akinbender/open-smartwatch-spy/3d/rugged box/stls/hinge v1.STL

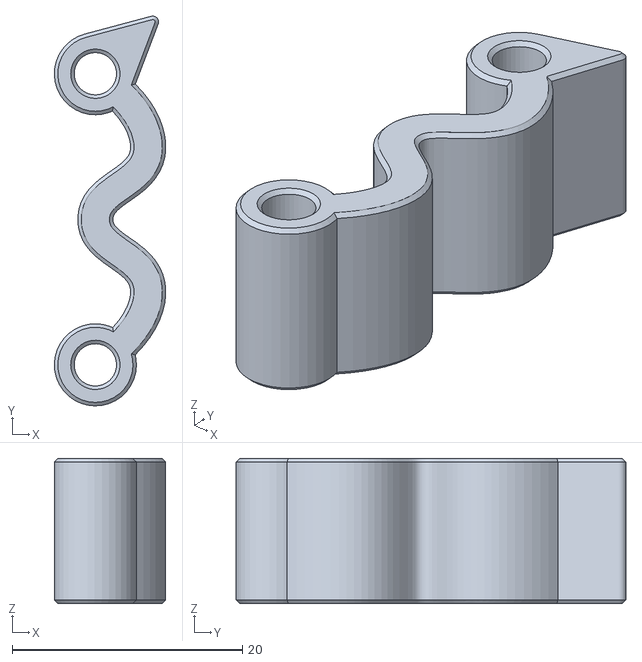
[picture p15: CAD file, 2022-03-14]
3d/rugged box/stls/hinge v1.STL
9.68 x 33.9 x 12.6
