akinbender/open-smartwatch-spy/3d/spywatch/bottom_subassembly/bottom_shell.SLDPRT

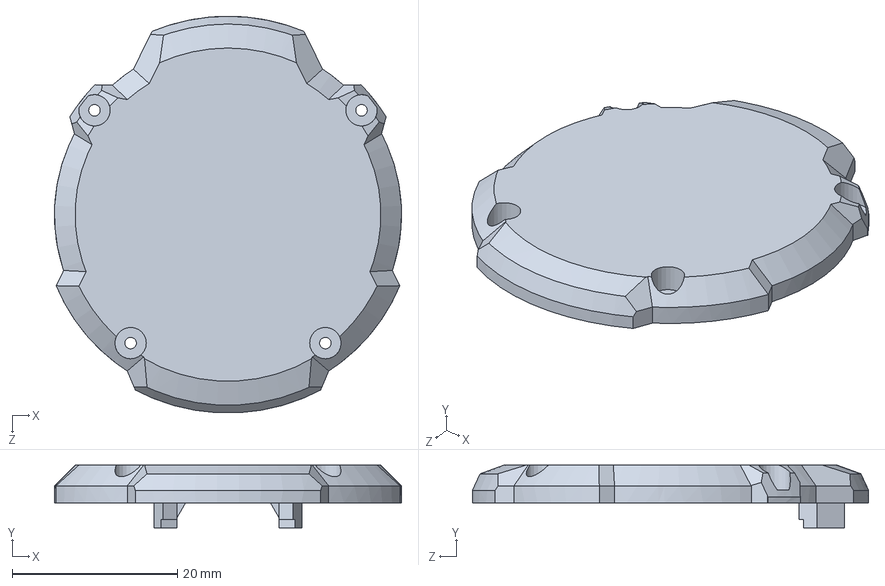
[picture p16: CAD file, 2022-03-14]
3d/spywatch/bottom_subassembly/bottom_shell.SLDPRT
42.0 x 7.60 x 48.0 mm
