akinbender/open-smartwatch-spy/3d/spywatch/common/middle_payload_test.SLDPRT

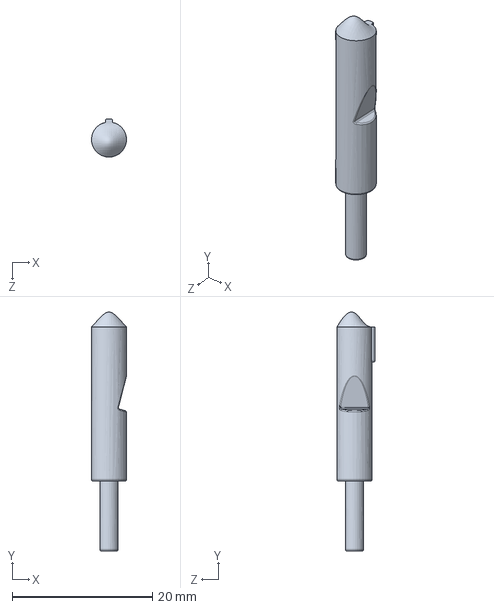
[picture p17: CAD file, 2022-03-14]
3d/spywatch/common/middle_payload_test.SLDPRT
5.00 x 34.1 x 5.45 mm
