akinbender/open-smartwatch-spy/3d/spywatch/middle_subassembly_fail1/middle_release_trigger.SLDPRT

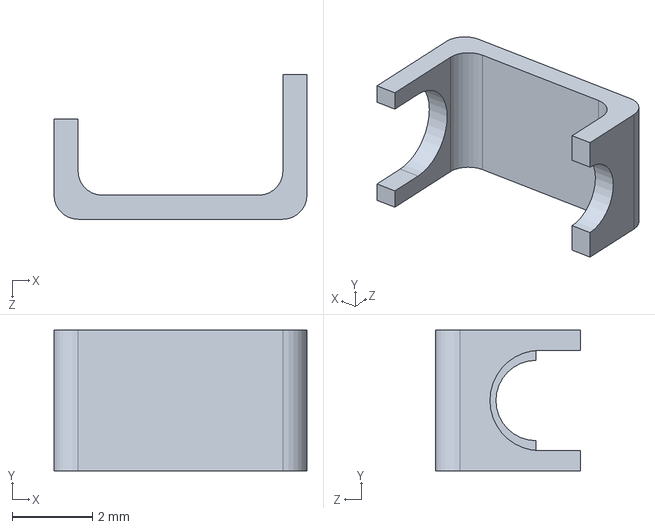
[picture p18: CAD file, 2022-03-14]
3d/spywatch/middle_subassembly_fail1/middle_release_trigger.SLDPRT
6.30 x 3.50 x 3.60 mm
