akinbender/open-smartwatch-spy/3d/spywatch/middle_subassembly_fail1/stl/middle_payload_dart.STL

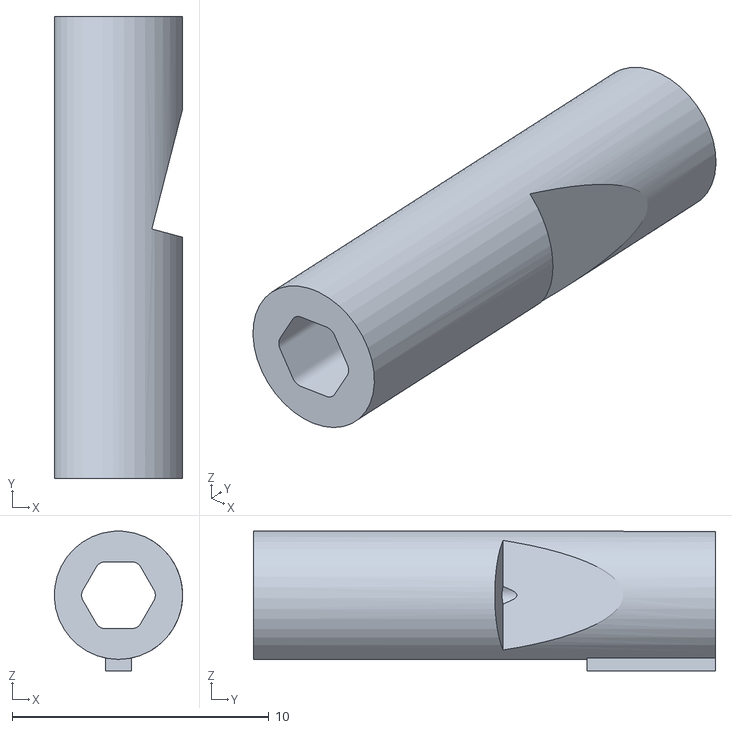
[picture p19: CAD file, 2022-03-14]
3d/spywatch/middle_subassembly_fail1/stl/middle_payload_dart.STL
5.00 x 18.0 x 5.45
