akinbender/open-smartwatch-spy/3d/spywatch/top_subassembly/top_lcd.SLDPRT

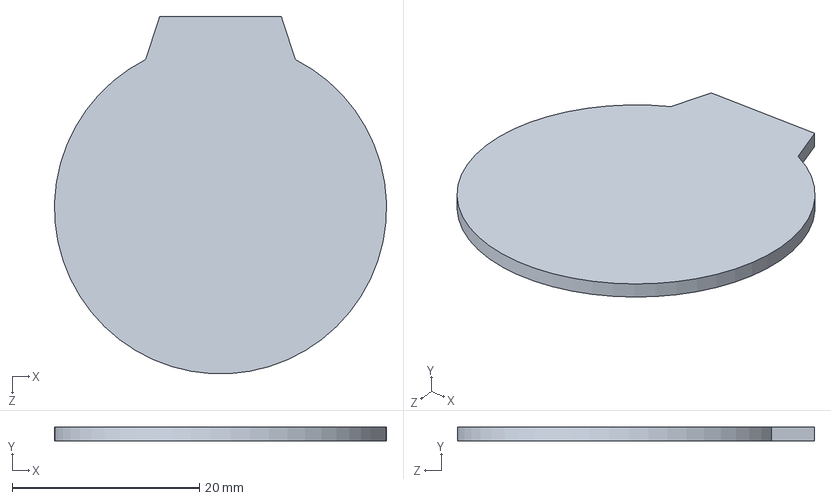
[picture p20: CAD file, 2022-03-14]
3d/spywatch/top_subassembly/top_lcd.SLDPRT
35.5 x 1.50 x 38.2 mm
