akinbender/open-smartwatch-spy/3d/rugged box/stls/latch cam v1.STL

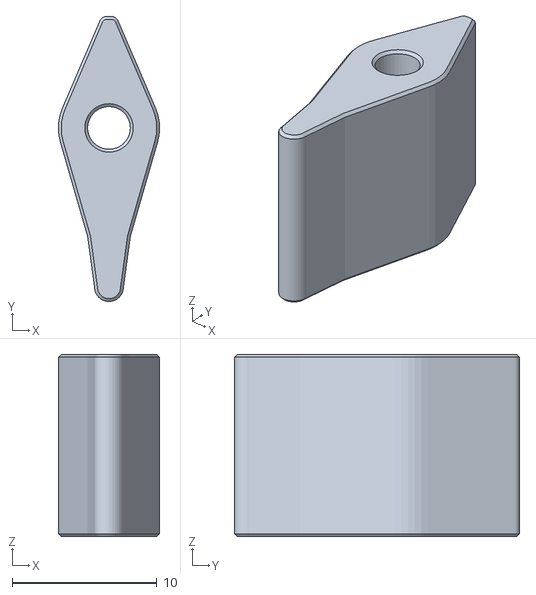
[picture p21: CAD file, 2022-03-14]
3d/rugged box/stls/latch cam v1.STL
7.00 x 19.7 x 12.6
