akinbender/open-smartwatch-spy/3d/spywatch/common/middle_osw_board.SLDPRT

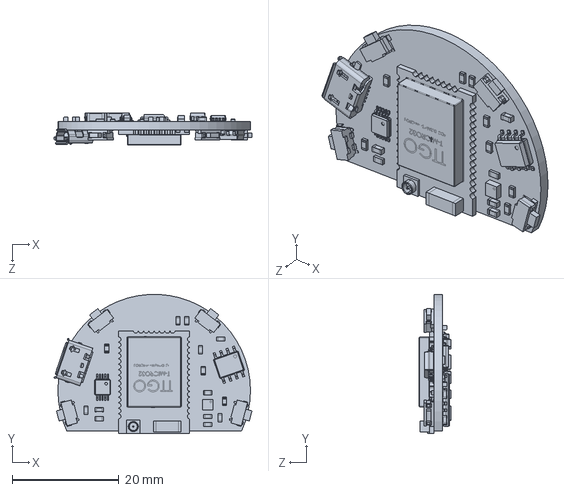
[picture p22: CAD file, 2022-03-14]
3d/spywatch/common/middle_osw_board.SLDPRT
37.0 x 26.0 x 6.00 mm
