akinbender/open-smartwatch-spy/3d/spywatch/middle_subassembly_fail1/middle_shell.SLDPRT

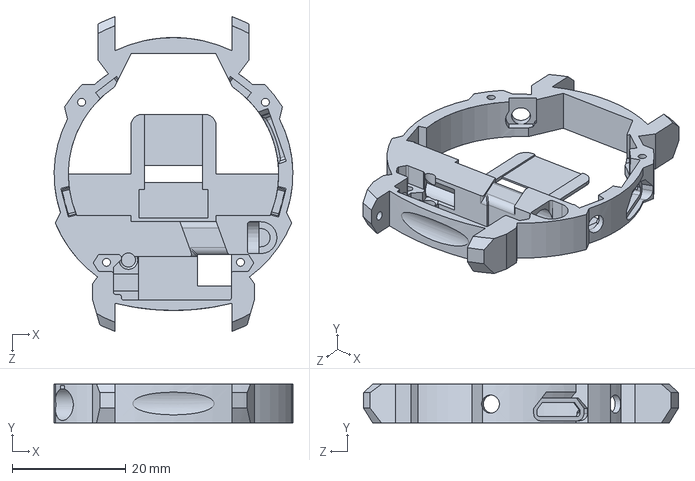
[picture p23: CAD file, 2022-03-14]
3d/spywatch/middle_subassembly_fail1/middle_shell.SLDPRT
42.0 x 6.80 x 55.4 mm
