akinbender/open-smartwatch-spy/3d/spywatch/middle_subassembly_fail1/stl/middle_payload_test.STL

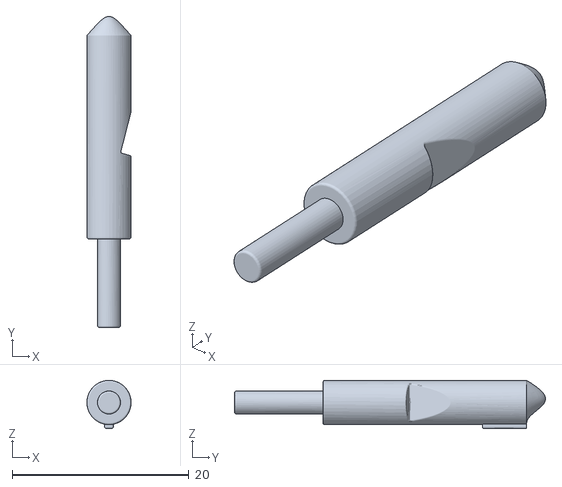
[picture p24: CAD file, 2022-03-14]
3d/spywatch/middle_subassembly_fail1/stl/middle_payload_test.STL
5.00 x 35.1 x 5.45
