akinbender/open-smartwatch-spy/3d/spywatch/middle_subassembly_manual/middle_release_trigger_button.SLDPRT

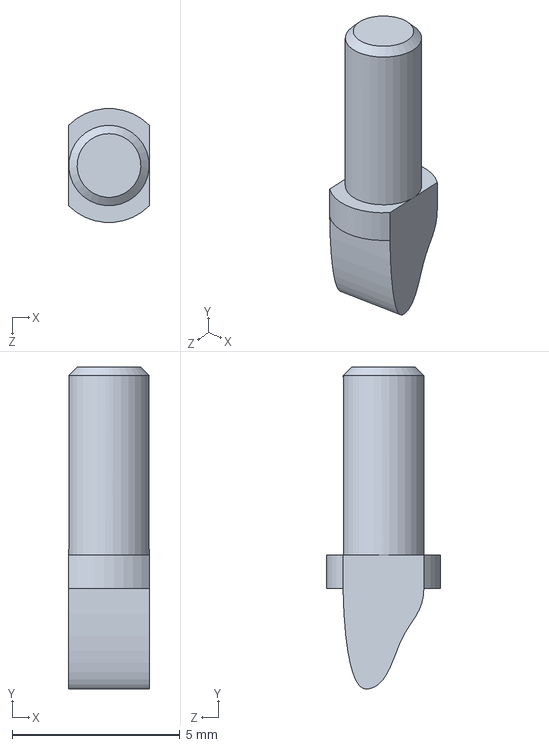
[picture p25: CAD file, 2022-03-14]
3d/spywatch/middle_subassembly_manual/middle_release_trigger_button.SLDPRT
2.40 x 9.60 x 3.39 mm
