akinbender/open-smartwatch-spy/3d/spywatch/top_subassembly/top_shell.SLDPRT

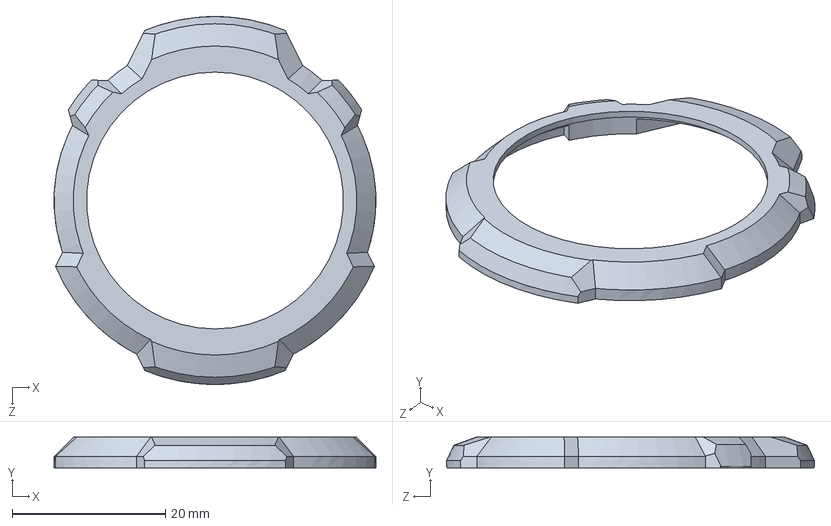
[picture p26: CAD file, 2022-03-14]
3d/spywatch/top_subassembly/top_shell.SLDPRT
42.0 x 4.00 x 48.0 mm
