akinbender/open-smartwatch-spy/3d/rugged box/box_top.SLDPRT

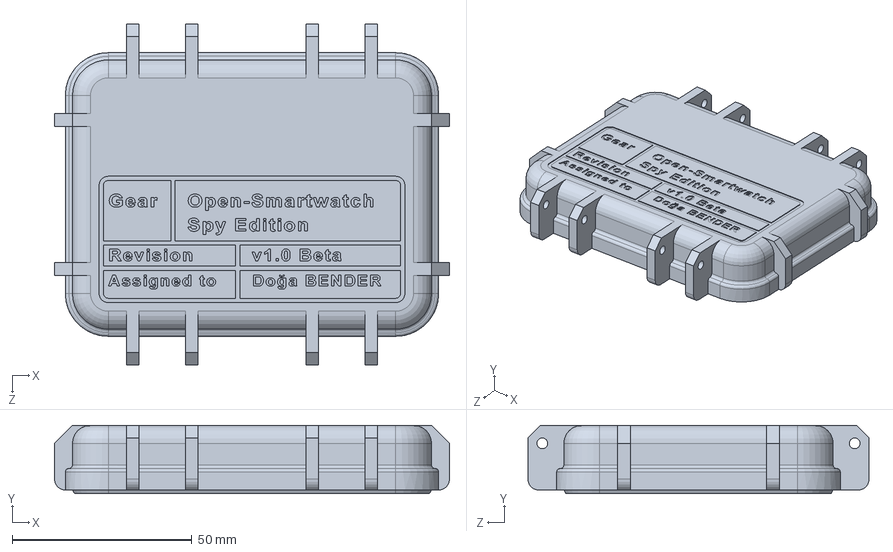
[picture p27: CAD file, 2022-03-14]
3d/rugged box/box_top.SLDPRT
110.0 x 19.0 x 95.0 mm
