akinbender/open-smartwatch-spy/3d/spywatch/middle_subassembly_fail1/middle_release_spring.SLDPRT

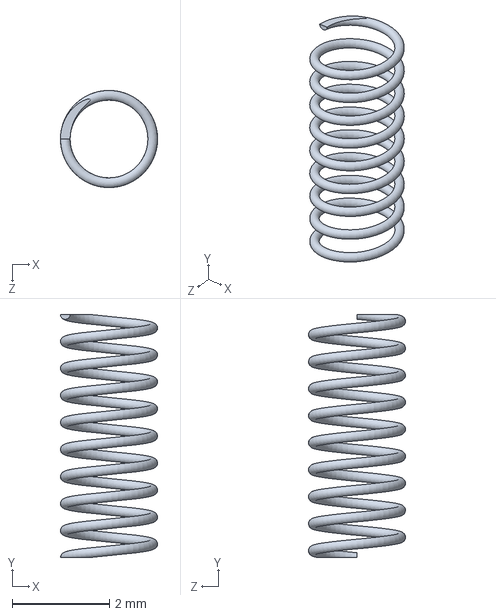
[picture p28: CAD file, 2022-03-14]
3d/spywatch/middle_subassembly_fail1/middle_release_spring.SLDPRT
2.00 x 5.00 x 2.00 mm
