akinbender/open-smartwatch-spy/3d/spywatch/middle_subassembly_manual/middle_release_pin_connector.SLDPRT

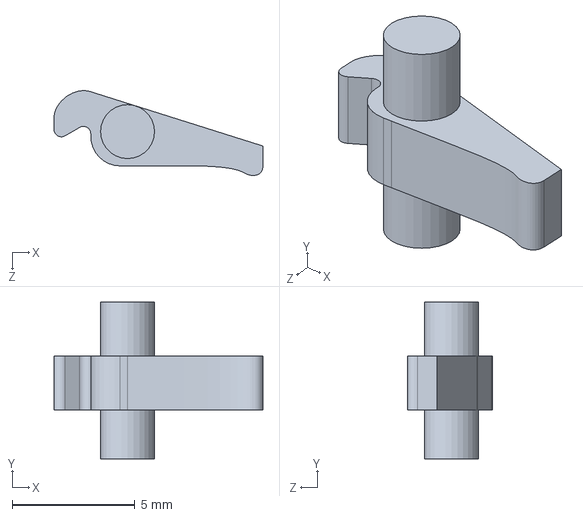
[picture p29: CAD file, 2022-03-14]
3d/spywatch/middle_subassembly_manual/middle_release_pin_connector.SLDPRT
8.52 x 6.40 x 3.46 mm
