akinbender/open-smartwatch-spy/3d/spywatch/top_subassembly/top_shell_inner.SLDPRT

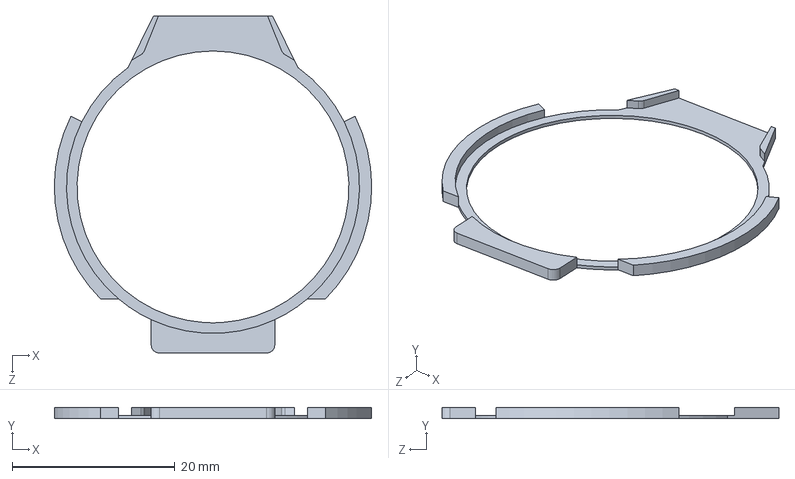
[picture p30: CAD file, 2022-03-14]
3d/spywatch/top_subassembly/top_shell_inner.SLDPRT
39.0 x 1.40 x 41.4 mm
