akinbender/open-smartwatch-spy/3d/spywatch/common/middle_button_short.SLDPRT

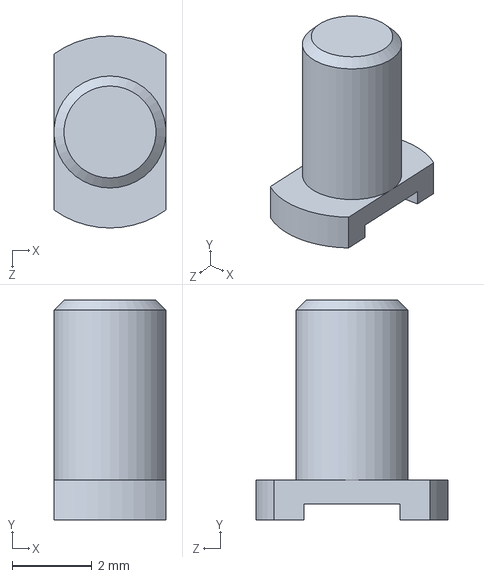
[picture p31: CAD file, 2022-03-14]
3d/spywatch/common/middle_button_short.SLDPRT
2.80 x 5.50 x 4.80 mm
