akinbender/open-smartwatch-spy/3d/spywatch/top_subassembly/top_glass.SLDPRT

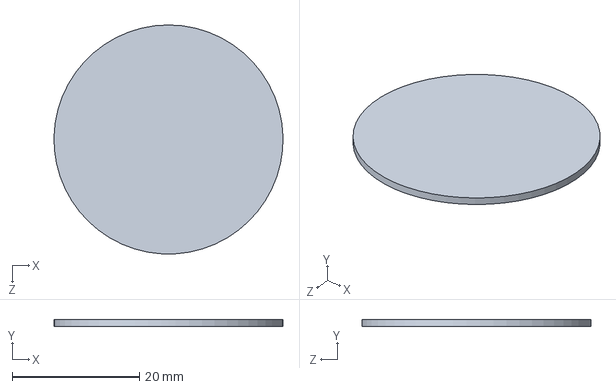
[picture p32: CAD file, 2022-03-14]
3d/spywatch/top_subassembly/top_glass.SLDPRT
36.0 x 1.10 x 36.0 mm
