akinbender/open-smartwatch-spy/3d/rugged box/box_bottom.SLDPRT

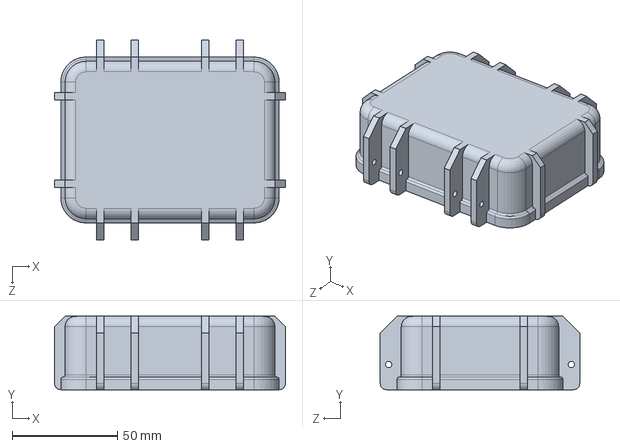
[picture p33: CAD file, 2022-03-14]
3d/rugged box/box_bottom.SLDPRT
110.0 x 35.0 x 95.0 mm
