akinbender/open-smartwatch-spy/3d/spywatch/middle_subassembly_fail1/middle_payload_spring.SLDPRT

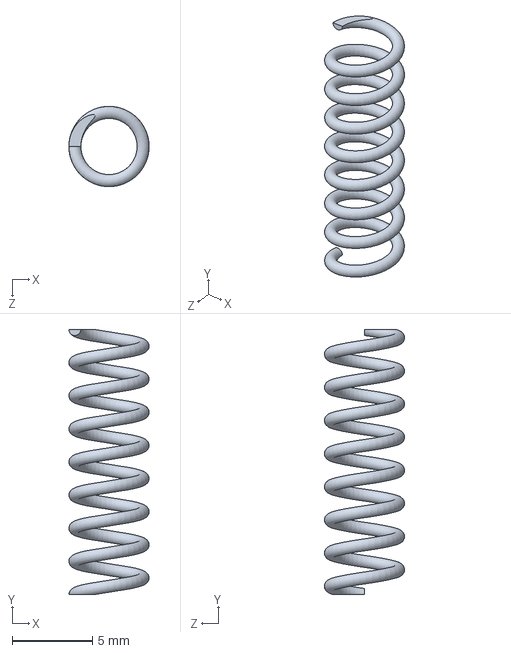
[picture p34: CAD file, 2022-03-14]
3d/spywatch/middle_subassembly_fail1/middle_payload_spring.SLDPRT
5.00 x 16.5 x 5.00 mm
