akinbender/open-smartwatch-spy/3d/spywatch/middle_subassembly_manual/middle_release_cover.SLDPRT

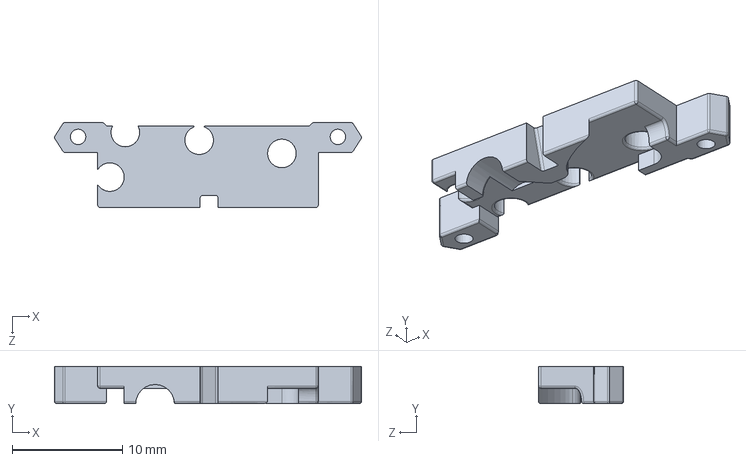
[picture p35: CAD file, 2022-03-14]
3d/spywatch/middle_subassembly_manual/middle_release_cover.SLDPRT
27.8 x 3.40 x 7.70 mm
