akinbender/open-smartwatch-spy/3d/spywatch/common/middle_servo.SLDPRT

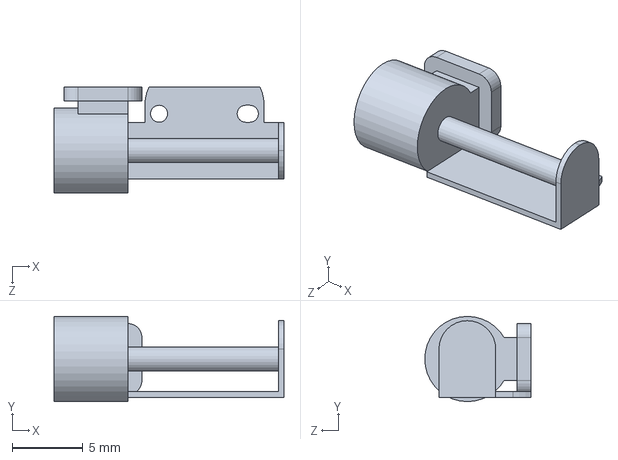
[picture p36: CAD file, 2022-03-14]
3d/spywatch/common/middle_servo.SLDPRT
16.2 x 6.00 x 7.50 mm
