akinbender/open-smartwatch-spy/3d/spywatch/middle_subassembly_fail1/middle_release_cover.SLDPRT

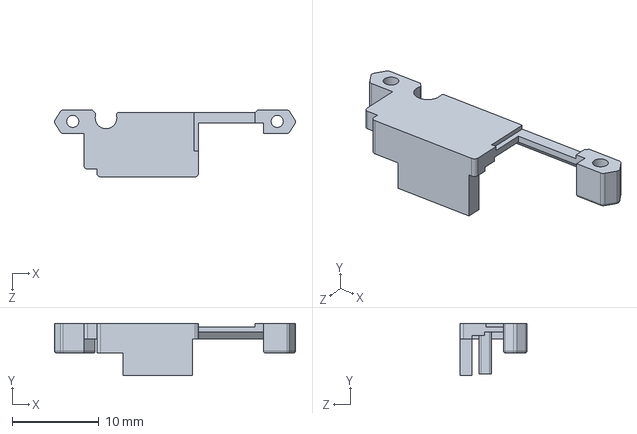
[picture p37: CAD file, 2022-03-14]
3d/spywatch/middle_subassembly_fail1/middle_release_cover.SLDPRT
27.8 x 6.00 x 7.70 mm
