akinbender/open-smartwatch-spy/3d/spywatch/middle_subassembly_manual/middle_case.SLDPRT

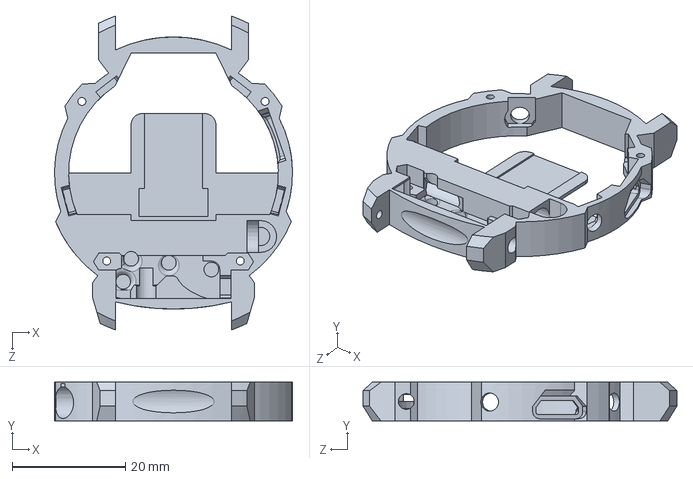
[picture p38: CAD file, 2022-03-14]
3d/spywatch/middle_subassembly_manual/middle_case.SLDPRT
42.0 x 6.80 x 55.4 mm
