akinbender/open-smartwatch-spy/3d/spywatch/common/stencil_aligner.SLDPRT

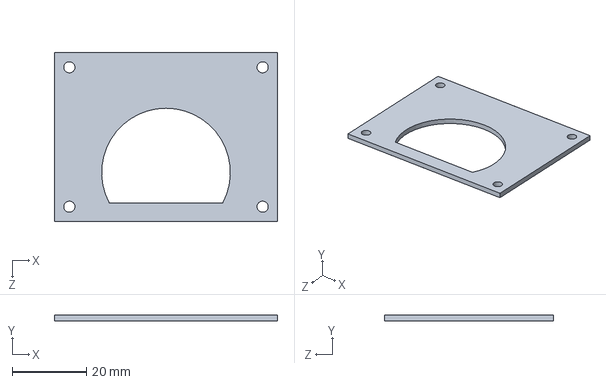
[picture p39: CAD file, 2022-03-14]
3d/spywatch/common/stencil_aligner.SLDPRT
60.0 x 1.60 x 45.5 mm
