akinbender/open-smartwatch-spy/3d/spywatch/middle_subassembly_manual/middle_release_pin.SLDPRT

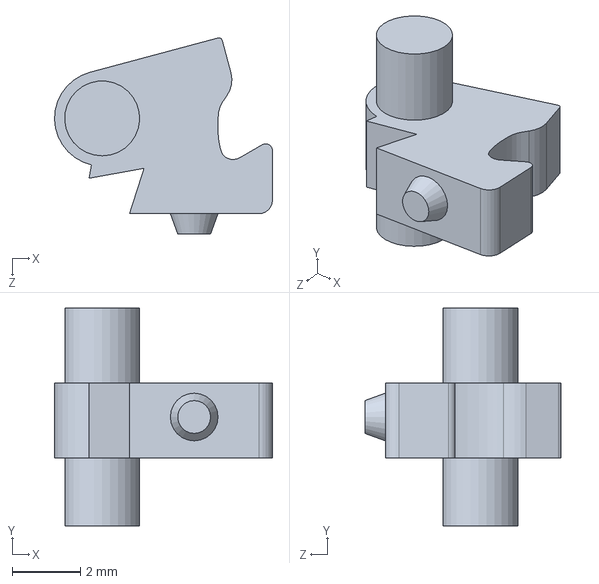
[picture p40: CAD file, 2022-03-14]
3d/spywatch/middle_subassembly_manual/middle_release_pin.SLDPRT
6.40 x 6.40 x 5.77 mm
