akinbender/open-smartwatch-spy/3d/spywatch/middle_subassembly_manual/middle_release_trigger_connector.SLDPRT

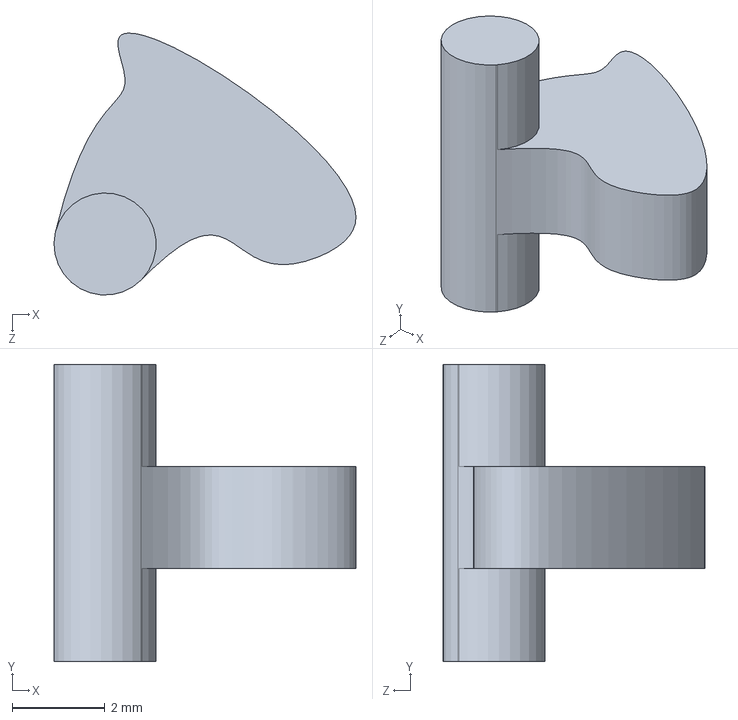
[picture p41: CAD file, 2022-03-14]
3d/spywatch/middle_subassembly_manual/middle_release_trigger_connector.SLDPRT
6.51 x 6.40 x 5.64 mm
