akinbender/open-smartwatch-spy/3d/spywatch/middle_subassembly_manual/middle_release_safety_pin.SLDPRT

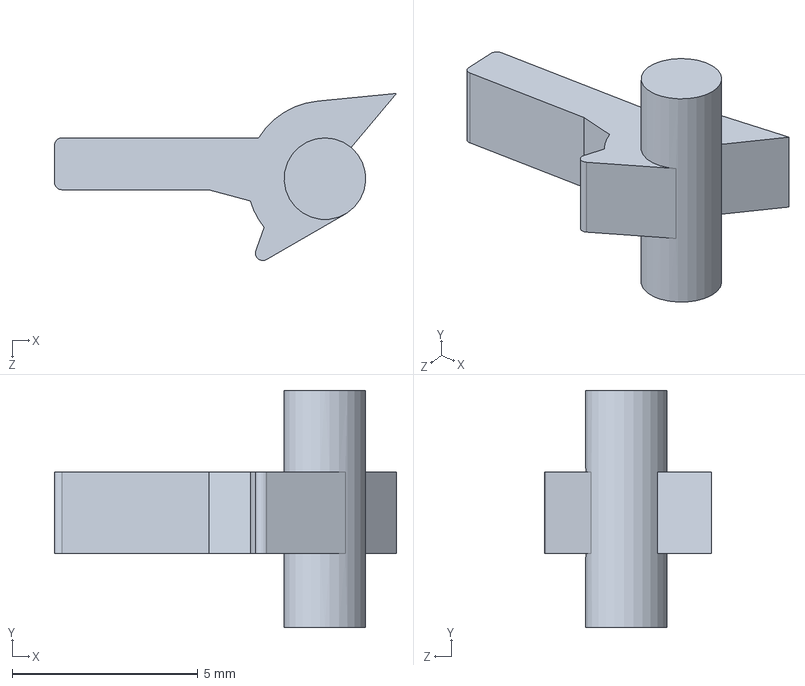
[picture p42: CAD file, 2022-03-14]
3d/spywatch/middle_subassembly_manual/middle_release_safety_pin.SLDPRT
9.22 x 6.40 x 4.50 mm
