akinbender/open-smartwatch-spy/3d/rugged box/box_bottom_payload_holder.SLDPRT

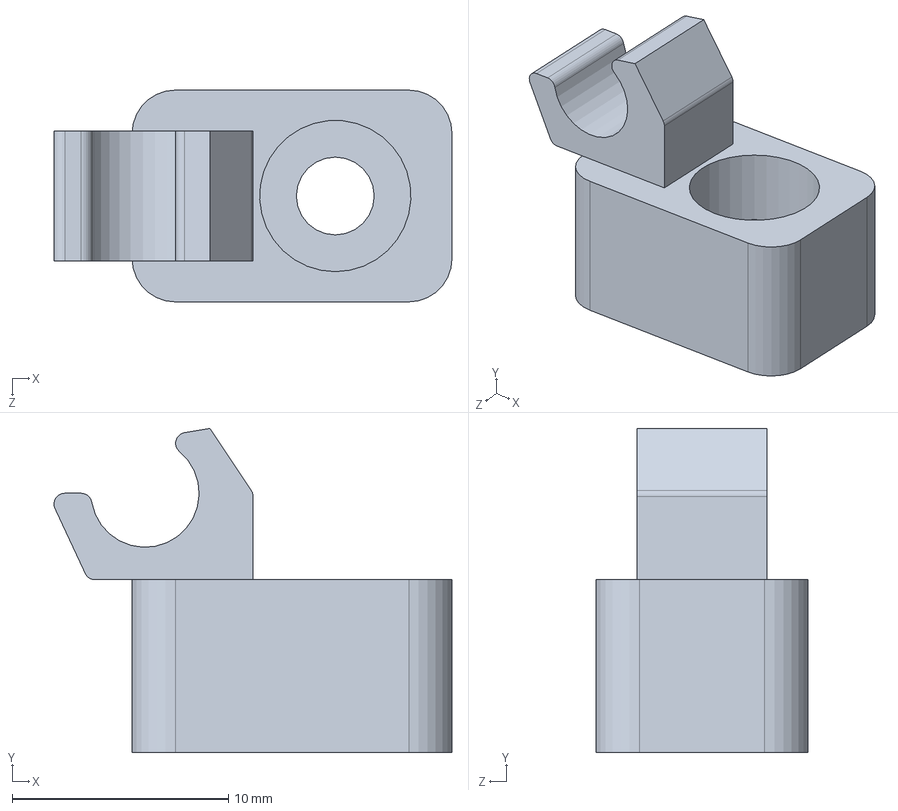
[picture p43: CAD file, 2022-03-14]
3d/rugged box/box_bottom_payload_holder.SLDPRT
18.4 x 15.0 x 9.80 mm
